platanus-hack/platanus-hack-26-co-team-28/lora-emergencia/center/MAP_DATA.md

# Cartografía offline de Bogotá

El mapa local se deriva exclusivamente de:

`https://download.geofabrik.de/south-america/colombia-shortbread-1.0.mbtiles`

- Datos: © OpenStreetMap contributors, publicados bajo ODbL 1.0.
- Distribución/procesamiento: Geofabrik GmbH.
- Esquema vectorial: Shortbread 1.0 (CC0); zoom nativo máximo 14.
- Recorte operacional: Bogotá urbana (`-74.25,4.45,-73.95,4.85`), zooms 11–14 y overzoom visual hasta 16.

La atribución `© OpenStreetMap contributors · Geofabrik` permanece visible en Leaflet. Consulta las condiciones originales en:

- https://www.openstreetmap.org/copyright
- https://download.geofabrik.de/
- https://shortbread-tiles.org/copyright/

El archivo generado `maps/bogota-shortbread.mbtiles` es un artefacto local ignorado por Git. La fuente completa de Colombia y los archivos parciales también están ignorados; la fuente se elimina después de un recorte exitoso.
